keebio/bfo9000-pcb/bfo9000.kicad_sch

## KiCad design bfo9000.kicad_sch (2025-01-17)

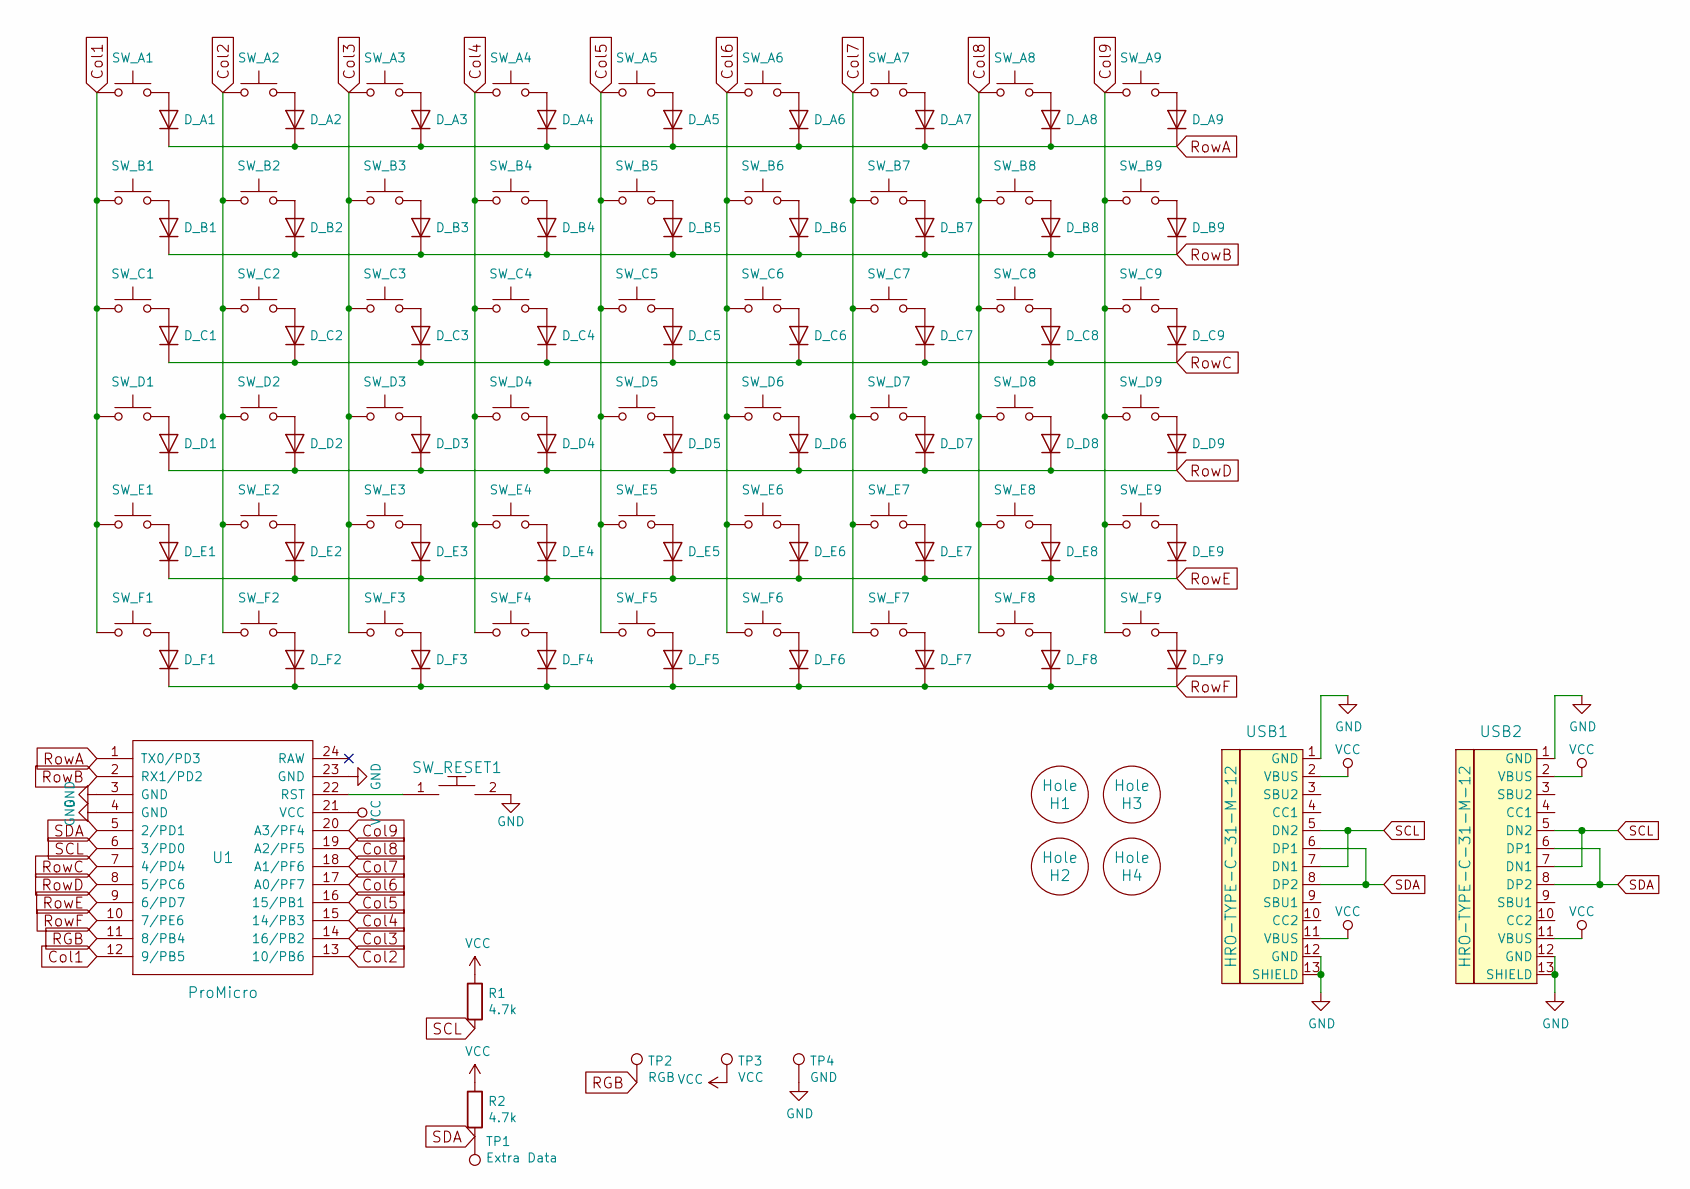
[picture p3: schematic bfo9000.kicad_sch]

Parts:
D_A1, D_A2, D_A3, D_A4, D_A5, D_A6, D_A7, D_A8, D_A9: D; Diode-Hybrid-Back
D_B1, D_B2, D_B3, D_B4, D_B5, D_B6, D_B7, D_B8, D_B9: D; Diode-Hybrid-Back
D_C1, D_C2, D_C3, D_C4, D_C5, D_C6, D_C7, D_C8, D_C9: D; Diode-Hybrid-Back
D_D1, D_D2, D_D3, D_D4, D_D5, D_D6, D_D7, D_D8, D_D9: D; Diode-Hybrid-Back
D_E1, D_E2, D_E3, D_E4, D_E5, D_E6, D_E7, D_E8, D_E9: D; Diode-Hybrid-Back
D_F1, D_F2, D_F3, D_F4, D_F5, D_F6, D_F7, D_F8, D_F9: D; Diode-Hybrid-Back
H1, H2, H3, H4: Hole; MountingHole_4mm
R1, R2: 4.7k; R_0603
SW_A1, SW_A2, SW_A3, SW_A4, SW_A5, SW_A6, SW_A7, SW_A8, SW_A9: SW_Push; MX-Alps-Choc_V1V2_KS-33-1U-NoLED-Alt
SW_B1, SW_B2, SW_B3, SW_B4, SW_B5, SW_B6, SW_B7, SW_B8, SW_B9: SW_Push; MX-Alps-Choc_V1V2_KS-33-1U-NoLED-Alt
SW_C1, SW_C2, SW_C3, SW_C4, SW_C5, SW_C6, SW_C7, SW_C8, SW_C9: SW_Push; MX-Alps-Choc_V1V2_KS-33-1U-NoLED-Alt
SW_D1, SW_D2, SW_D3, SW_D4, SW_D5, SW_D6, SW_D7, SW_D8, SW_D9: SW_Push; MX-Alps-Choc_V1V2_KS-33-1U-NoLED-Alt
SW_E1, SW_E2, SW_E3, SW_E4, SW_E5, SW_E6, SW_E7, SW_E8, SW_E9: SW_Push; MX-Alps-Choc_V1V2_KS-33-1U-NoLED-Alt
SW_F1, SW_F2, SW_F3, SW_F4, SW_F5, SW_F6, SW_F7, SW_F8, SW_F9: SW_Push; MX-Alps-Choc_V1V2_KS-33-1U-NoLED-Alt
SW_RESET1: Reset; SW_SPST_TL3342
TP1: Extra Data; SinglePad
TP2: RGB; SinglePad
TP3: VCC; SinglePad
TP4: GND; SinglePad
U1: ProMicro; ArduinoProMicro-ZigZag
USB1, USB2: HRO-TYPE-C-31-M-12; HRO-TYPE-C-31-M-12-Assembly

Connections:
Col1: SW_A1.1, SW_B1.1, SW_C1.1, SW_D1.1, SW_E1.1, SW_F1.1, U1.12 (9/PB5)
Col2: SW_A2.1, SW_B2.1, SW_C2.1, SW_D2.1, SW_E2.1, SW_F2.1, U1.13 (10/PB6)
Col3: SW_A3.1, SW_B3.1, SW_C3.1, SW_D3.1, SW_E3.1, SW_F3.1, U1.14 (16/PB2)
Col4: SW_A4.1, SW_B4.1, SW_C4.1, SW_D4.1, SW_E4.1, SW_F4.1, U1.15 (14/PB3)
Col5: SW_A5.1, SW_B5.1, SW_C5.1, SW_D5.1, SW_E5.1, SW_F5.1, U1.16 (15/PB1)
Col6: SW_A6.1, SW_B6.1, SW_C6.1, SW_D6.1, SW_E6.1, SW_F6.1, U1.17 (A0/PF7)
Col7: SW_A7.1, SW_B7.1, SW_C7.1, SW_D7.1, SW_E7.1, SW_F7.1, U1.18 (A1/PF6)
Col8: SW_A8.1, SW_B8.1, SW_C8.1, SW_D8.1, SW_E8.1, SW_F8.1, U1.19 (A2/PF5)
Col9: SW_A9.1, SW_B9.1, SW_C9.1, SW_D9.1, SW_E9.1, SW_F9.1, U1.20 (A3/PF4)
GND: SW_RESET1.2, TP4.1, U1.3 (GND), U1.4 (GND), U1.23 (GND), USB1.1 (GND), USB1.12 (GND), USB1.13 (SHIELD), USB2.1 (GND), USB2.12 (GND), USB2.13 (SHIELD)
unnamed: D_A1.2 (A), SW_A1.2
unnamed: D_A2.2 (A), SW_A2.2
unnamed: D_A3.2 (A), SW_A3.2
unnamed: D_A4.2 (A), SW_A4.2
unnamed: D_A5.2 (A), SW_A5.2
unnamed: D_A6.2 (A), SW_A6.2
unnamed: D_A7.2 (A), SW_A7.2
unnamed: D_A8.2 (A), SW_A8.2
unnamed: D_A9.2 (A), SW_A9.2
unnamed: D_B1.2 (A), SW_B1.2
unnamed: D_B2.2 (A), SW_B2.2
unnamed: D_B3.2 (A), SW_B3.2
unnamed: D_B4.2 (A), SW_B4.2
unnamed: D_B5.2 (A), SW_B5.2
unnamed: D_B6.2 (A), SW_B6.2
unnamed: D_B7.2 (A), SW_B7.2
unnamed: D_B8.2 (A), SW_B8.2
unnamed: D_B9.2 (A), SW_B9.2
unnamed: D_C1.2 (A), SW_C1.2
unnamed: D_C2.2 (A), SW_C2.2
unnamed: D_C3.2 (A), SW_C3.2
unnamed: D_C4.2 (A), SW_C4.2
unnamed: D_C5.2 (A), SW_C5.2
unnamed: D_C6.2 (A), SW_C6.2
unnamed: D_C7.2 (A), SW_C7.2
unnamed: D_C8.2 (A), SW_C8.2
unnamed: D_C9.2 (A), SW_C9.2
unnamed: D_D1.2 (A), SW_D1.2
unnamed: D_D2.2 (A), SW_D2.2
unnamed: D_D3.2 (A), SW_D3.2
unnamed: D_D4.2 (A), SW_D4.2
unnamed: D_D5.2 (A), SW_D5.2
unnamed: D_D6.2 (A), SW_D6.2
unnamed: D_D7.2 (A), SW_D7.2
unnamed: D_D8.2 (A), SW_D8.2
unnamed: D_D9.2 (A), SW_D9.2
unnamed: D_E1.2 (A), SW_E1.2
unnamed: D_E2.2 (A), SW_E2.2
unnamed: D_E3.2 (A), SW_E3.2
unnamed: D_E4.2 (A), SW_E4.2
unnamed: D_E5.2 (A), SW_E5.2
unnamed: D_E6.2 (A), SW_E6.2
unnamed: D_E7.2 (A), SW_E7.2
unnamed: D_E8.2 (A), SW_E8.2
unnamed: D_E9.2 (A), SW_E9.2
unnamed: D_F1.2 (A), SW_F1.2
unnamed: D_F2.2 (A), SW_F2.2
unnamed: D_F3.2 (A), SW_F3.2
unnamed: D_F4.2 (A), SW_F4.2
unnamed: D_F5.2 (A), SW_F5.2
unnamed: D_F6.2 (A), SW_F6.2
unnamed: D_F7.2 (A), SW_F7.2
unnamed: D_F8.2 (A), SW_F8.2
unnamed: D_F9.2 (A), SW_F9.2
unnamed: SW_RESET1.1, U1.22 (RST)
RGB: TP2.1, U1.11 (8/PB4)
RowA: D_A1.1 (K), D_A2.1 (K), D_A3.1 (K), D_A4.1 (K), D_A5.1 (K), D_A6.1 (K), D_A7.1 (K), D_A8.1 (K), D_A9.1 (K), U1.1 (TX0/PD3)
RowB: D_B1.1 (K), D_B2.1 (K), D_B3.1 (K), D_B4.1 (K), D_B5.1 (K), D_B6.1 (K), D_B7.1 (K), D_B8.1 (K), D_B9.1 (K), U1.2 (RX1/PD2)
RowC: D_C1.1 (K), D_C2.1 (K), D_C3.1 (K), D_C4.1 (K), D_C5.1 (K), D_C6.1 (K), D_C7.1 (K), D_C8.1 (K), D_C9.1 (K), U1.7 (4/PD4)
RowD: D_D1.1 (K), D_D2.1 (K), D_D3.1 (K), D_D4.1 (K), D_D5.1 (K), D_D6.1 (K), D_D7.1 (K), D_D8.1 (K), D_D9.1 (K), U1.8 (5/PC6)
RowE: D_E1.1 (K), D_E2.1 (K), D_E3.1 (K), D_E4.1 (K), D_E5.1 (K), D_E6.1 (K), D_E7.1 (K), D_E8.1 (K), D_E9.1 (K), U1.9 (6/PD7)
RowF: D_F1.1 (K), D_F2.1 (K), D_F3.1 (K), D_F4.1 (K), D_F5.1 (K), D_F6.1 (K), D_F7.1 (K), D_F8.1 (K), D_F9.1 (K), U1.10 (7/PE6)
SCL: R1.2, U1.6 (3/PD0), USB1.5 (DN2), USB1.7 (DN1), USB2.5 (DN2), USB2.7 (DN1)
SDA: R2.2, TP1.1, U1.5 (2/PD1), USB1.6 (DP1), USB1.8 (DP2), USB2.6 (DP1), USB2.8 (DP2)
VCC: R1.1, R2.1, TP3.1, U1.21 (VCC), USB1.2 (VBUS), USB1.11 (VBUS), USB2.2 (VBUS), USB2.11 (VBUS)
